Pollex/MFM4-EZO-EC-2/modules/ezoec/ezoec.c

#include "include/ezoec.h"
#include "mutex.h"
#include "periph/uart.h"
#include "thread.h"
#include "thread_flags.h"
#include "tsrb.h"
#include "ztimer.h"
#include <stdarg.h>
#include <stdint.h>
#include <stdio.h>
#include <string.h>
#include <sys/errno.h>

#define ENABLE_DEBUG 0
#include "debug.h"

#define ASSERT_OK_TIMEOUT 2500
#define TX_MAX_LINE_LEN   42
#define MAX_DECIMALS      3
#define DEV               UART_DEV(ec->params.uart)

char *_int_to_string(uint8_t k, uint8_t precision);

enum {
    STATUS_OK,
    STATUS_ERROR,
    STATUS_OVERVOLT,
    STATUS_UNDERVOLT,
    STATUS_RESET,
    STATUS_READY,
    STATUS_SLEEP,
    STATUS_WAKE,
    STATUS_DONE,
} status_t;

#define MAX_STATUS_LEN 6
static int _read_status(ezoec_t *ec, uint32_t timeout) {
    // Wait for first status messsage (prefixed by *)
    while (!tsrb_empty(&ec->rx_ringbuffer) && tsrb_peek_one(&ec->rx_ringbuffer) != '*') {
        tsrb_get_one(&ec->rx_ringbuffer);
    }

    char status[MAX_STATUS_LEN] = {0};
    int len                     = ezoec_readline(ec, status, MAX_STATUS_LEN, timeout);
    if (len < 0) {
        return len;
    }
    DEBUG("[%s]: %s\n", __func__, status);
    if (strcmp(status, "*OK") == 0)
        return STATUS_OK;
    if (strcmp(status, "*ER") == 0)
        return STATUS_ERROR;
    if (strcmp(status, "*OV") == 0)
        return STATUS_OVERVOLT;
    if (strcmp(status, "*UV") == 0)
        return STATUS_UNDERVOLT;
    if (strcmp(status, "*RS") == 0)
        return STATUS_RESET;
    if (strcmp(status, "*RE") == 0)
        return STATUS_READY;
    if (strcmp(status, "*SL") == 0)
        return STATUS_SLEEP;
    if (strcmp(status, "*WA") == 0)
        return STATUS_WAKE;
    if (strcmp(status, "*DONE") == 0)
        return STATUS_DONE;
    return -1;
}

#define FLAG_RX_DATA (1u << 0)
static void on_ezoec_receive(void *arg, uint8_t data) {
    ezoec_t *ec = (ezoec_t *)arg;
    tsrb_add_one(&ec->rx_ringbuffer, data);
    thread_flags_set(thread_get(ec->rx_thread), FLAG_RX_DATA);
}

int ezoec_init(ezoec_t *ec, const ezoec_params_t *params) {
    ec->params = *params;
    mutex_init(&ec->readline_lock);

    tsrb_init(&ec->rx_ringbuffer, ec->rx_buffer, sizeof(ec->rx_buffer));

    int result = uart_init(DEV, ec->params.baud_rate, on_ezoec_receive, ec);
    if (result < 0) {
        DEBUG("[%s]: Could not init uart at %d: %d\n", __func__, ec->params.baud_rate, result);
        return result;
    }
    uart_write(DEV, (const uint8_t *)"\r", 1);
    ezoec_assert_ok(ec);

    char version[15] = {0};
    result           = ezoec_cmd(ec, 500, version, sizeof(version), "i");
    if (result < 0) {
        DEBUG("[%s]: Could not get version: %d\n", __func__, result);
        return result;
    }
    if (result < 5) {
        DEBUG("[%s]: Not enough rx to be version info: %d\n", __func__, result);
        return -ENODEV;
    }
    if (version[3] != 'E' || version[4] != 'C') {
        DEBUG("[%s]: does not appear to be EC device: %s\n", __func__, version);
        return -ENODEV;
    }

    DEBUG("[%s]: Init success\n", __func__);
    return 0;
}

int ezoec_set_baud(ezoec_t *ec, unsigned int baud) { return ezoec_cmd(ec, 0, NULL, 0, "Baud,%d", baud); }

int ezoec_factory(ezoec_t *ec) {
    uart_write(DEV, (const uint8_t *)"Factory\r", sizeof("Factory\r"));

    int result = 0;
    // Wait for reset
    result = _read_status(ec, 2000);
    if (result < 0)
        return result;
    if (result != STATUS_OK)
        return -1;
    result = _read_status(ec, 2000);
    if (result < 0)
        return result;
    if (result != STATUS_RESET)
        return -1;
    result = _read_status(ec, 2000);
    if (result < 0)
        return result;
    if (result != STATUS_READY)
        return -1;

    DEBUG("[%s]: EZO ready\n", __func__);
    return 0;
}

int ezoec_set_k(ezoec_t *ec, uint8_t k_value) {
    return ezoec_cmd(ec, 0, NULL, 0, "K,%s", _int_to_string(k_value, 1));
}

int ezoec_measure(ezoec_t *ec, uint32_t *out_nS) {
    char rx[RX_MAX_LINE_LEN] = {0};
    int rx_len               = ezoec_cmd(ec, 2000, rx, sizeof(rx), "R");
    if (rx_len < 0) {
        return rx_len;
    }

    // Convert to int. Stop at first non-digit/non-dot so multi-field
    // responses (e.g. "100,54" when TDS is enabled) don't corrupt the
    // value by adding negative ASCII offsets to an unsigned accumulator.
    char *ptr_start = rx;
    char *ptr_end   = ptr_start + rx_len;
    char *ptr       = ptr_start;
    char *dot       = NULL;

    *out_nS = 0;
    while (ptr < ptr_end) {
        if (*ptr == '.') {
            if (dot != NULL) {
                return -EINVAL; // Second dot — malformed.
            }
            dot = ptr;
            ptr++;
            continue;
        }
        if (*ptr < '0' || *ptr > '9') {
            break;
        }

        *out_nS *= 10;
        *out_nS += (*ptr - 0x30);
        ptr++;
    }
    if (ptr == ptr_start) {
        return -EINVAL; // No digits parsed.
    }

    // Pad missing fractional digits to MAX_DECIMALS.
    uint8_t decimals = (dot == NULL) ? 0 : (uint8_t)(ptr - dot - 1);
    for (int x = MAX_DECIMALS - decimals; x > 0; x--) {
        *out_nS *= 10;
    }

    return 0;
}

int ezoec_is_calibrated(ezoec_t *ec) {
    char rx[RX_MAX_LINE_LEN] = {0};
    int result               = ezoec_cmd(ec, 100, rx, sizeof(rx), "Cal,?");
    if (result < 0) {
        return result;
    }
    return rx[5] - 0x30;
}

int ezoec_cal_dry(ezoec_t *ec) { return ezoec_cmd(ec, 0, NULL, 0, "Cal,dry"); }

int ezoec_cal_low(ezoec_t *ec, uint32_t uS) { return ezoec_cmd(ec, 0, NULL, 0, "Cal,low,%d", uS); }

int ezoec_cal_high(ezoec_t *ec, uint32_t uS) { return ezoec_cmd(ec, 0, NULL, 0, "Cal,high,%d", uS); }

int ezoec_cal_import(ezoec_t *ec, ezoec_calibration_t *cal) {
    int result = 0;
    for (int line = 0; line < EZOEC_CALIBRATION_MAX_LINES; line++) {
        result = ezoec_cmd(ec, 0, NULL, 0, "Import,%.12s", cal->line[line]);
        if (result < 0) {
            DEBUG("[%s]: Error importing: %d\n", __func__, result);
            return result;
        }
    }

    // Wait for reset
    char rxBuffer[13] = {0};
    result            = ezoec_readline(ec, rxBuffer, 12, 2000);
    if (result < 0) {
        DEBUG("[%s]: Error waiting for reset: %d\n", __func__, result);
        return result;
    }
    if (strcmp(rxBuffer, "*RS") != 0) {
        DEBUG("[%s]: Expected EZO reset\n", __func__);
        return 0;
    }
    DEBUG("[%s]: EZO resetting\n", __func__);

    result = ezoec_readline(ec, rxBuffer, 12, 2000);
    if (result < 0) {
        DEBUG("[%s]: Error waiting for ready: %d\n", __func__, result);
        return result;
    }
    if (strcmp(rxBuffer, "*RE") != 0) {
        DEBUG("[%s]: Expected EZO ready\n", __func__);
        return 0;
    }
    DEBUG("[%s]: EZO ready\n", __func__);

    return 0;
}

int ezoec_cal_export(ezoec_t *ec, ezoec_calibration_t *cal) {
    int result                                       = 0;
    char rxBuffer[EZOEC_CALIBRATION_LINE_LENGTH + 1] = {0};
    // Loop one extra iteration to consume the trailing *DONE line.
    for (int line = 0; line < EZOEC_CALIBRATION_MAX_LINES + 1; line++) {
        result = ezoec_cmd(ec, 1000, rxBuffer, sizeof(rxBuffer), "Export");
        if (result < 0) {
            DEBUG("[%s]: Error reading export: %d\n", __func__, result);
            return result;
        }
        if (result > EZOEC_CALIBRATION_LINE_LENGTH) {
            result = EZOEC_CALIBRATION_LINE_LENGTH;
        }
        rxBuffer[result] = 0;

        DEBUG("[%s]: Read %d bytes\n", __func__, result);
        if (strcmp(rxBuffer, "*DONE") == 0) {
            DEBUG("[%s]: Done with export\n", __func__);
            return line;
        }

        // Bounds-check before writing into the fixed-size calibration array.
        if (line >= EZOEC_CALIBRATION_MAX_LINES) {
            DEBUG("[%s]: Too many export lines, no *DONE seen\n", __func__);
            return -EOVERFLOW;
        }
        memcpy(cal->line[line], rxBuffer, result);
    }
    return -1;
}

//
int ezoec_writeline(ezoec_t *ec, const char *format, ...) {
    static char txbuf[TX_MAX_LINE_LEN] = {0};

    va_list args;
    va_start(args, format);
    int len = vsnprintf(txbuf, sizeof(txbuf) - 1, format, args);
    va_end(args);
    if (len < 0 || (size_t)len >= sizeof(txbuf) - 1) {
        return -EOVERFLOW;
    }
    txbuf[len++] = '\r';
    tsrb_clear(&ec->rx_ringbuffer);
    uart_write(DEV, (uint8_t *)txbuf, len);

    return 0;
}

int ezoec_cmd(ezoec_t *ec, uint32_t timeout, char *out, uint8_t out_len, const char *format, ...) {
    static char txbuf[TX_MAX_LINE_LEN] = {0};

    va_list args;
    va_start(args, format);
    int len = vsnprintf(txbuf, sizeof(txbuf) - 1, format, args);
    va_end(args);
    if (len < 0 || (size_t)len >= sizeof(txbuf) - 1) {
        return -EOVERFLOW;
    }
    txbuf[len++] = '\r';

    tsrb_clear(&ec->rx_ringbuffer);
    uart_write(DEV, (uint8_t *)txbuf, len);
#if ENABLE_DEBUG
    fwrite(txbuf, len, 1, stdout);
    putc('\n', stdout);
#endif

    // Only if out is given will we read a response
    int rx_len = 0;
    if (out != NULL) {
        rx_len = ezoec_readline(ec, out, out_len, timeout);
        if (rx_len < 0)
            return rx_len;
    }

    int result = ezoec_assert_ok(ec);
    if (result < 0)
        return result;

    return rx_len;
}

int ezoec_readline(ezoec_t *ec, char *buf, uint8_t buf_len, uint32_t timeout) {
    // Ensure only one readline function can be active at a time.
    mutex_lock(&ec->readline_lock);

    char *ptr = buf;

    int result = 0;
    ztimer_t timer;
    ec->rx_thread = thread_getpid();

    for (;;) {
        // If there is no uart data in the buffer, we'll wait for some to
        // appear, or timeout.
        if (tsrb_avail(&ec->rx_ringbuffer) == 0) {
            ztimer_set_timeout_flag(ZTIMER_MSEC, &timer, timeout);

            // Wait for flag and clear it. Returns the flags that were set.
            int flags = thread_flags_wait_any(FLAG_RX_DATA | THREAD_FLAG_TIMEOUT);

            // Make sure to remove the timer if it didn't fire already. Noop if
            // it did.
            ztimer_remove(ZTIMER_MSEC, &timer);

            // If there is no RX_DATA flag set, but it has timed out, we exit.
            if ((flags & FLAG_RX_DATA) == 0 && (flags & THREAD_FLAG_TIMEOUT) > 0) {
                result = -ETIMEDOUT;
                break;
            }
        }

        int data = tsrb_get_one(&ec->rx_ringbuffer);
        if (data < 0) {
            continue;
        }

        if (data == '\r') {
            result = ptr - buf;
#if ENABLE_DEBUG
            fwrite("<<< ", 4, 1, stdout);
            fwrite(buf, result, 1, stdout);
            putc('\n', stdout);
#endif
            break;
        }

        *ptr++ = data;
        if (ptr == buf + buf_len) {
            result = -ENOBUFS;
            break;
        }
    }

    mutex_unlock(&ec->readline_lock);
    return result;
}

int ezoec_assert_ok(ezoec_t *ec) {
    int result = 0;
read_status:
    result = _read_status(ec, ASSERT_OK_TIMEOUT);
    if (result < 0) {
        DEBUG("[%s]: Error reading status: %d\n", __func__, result);
        return result;
    }
    DEBUG("[%s]: Status: %d\n", __func__, result);
    switch (result) {
    case STATUS_OK:
        return 0;
    case STATUS_ERROR:
        return -1;
    case STATUS_OVERVOLT:
    case STATUS_UNDERVOLT:
    case STATUS_RESET:
    case STATUS_READY:
    case STATUS_SLEEP:
    case STATUS_WAKE:
        goto read_status;
    default:
        return -2;
    }
    return 0;
}

char *_int_to_string(uint8_t k, uint8_t precision) {
    enum { buf_len = 12 };
    static char buf[buf_len + 1] = {0};
    char *ptr                    = &buf[buf_len - 1];

    int decimals = 0;
    do {
        *ptr-- = 0x30 + (k % 10);
        k /= 10;
        if (++decimals == precision) {
            *ptr-- = '.';
            if (k == 0)
                *ptr-- = '0';
        }
    } while (k > 0 || decimals < precision);

    return ptr + 1;
}
